AmirAlsad/beta-rush-pcb-cards/docs/order-history/jlcpcb-p3-brother-pcb-spec.png

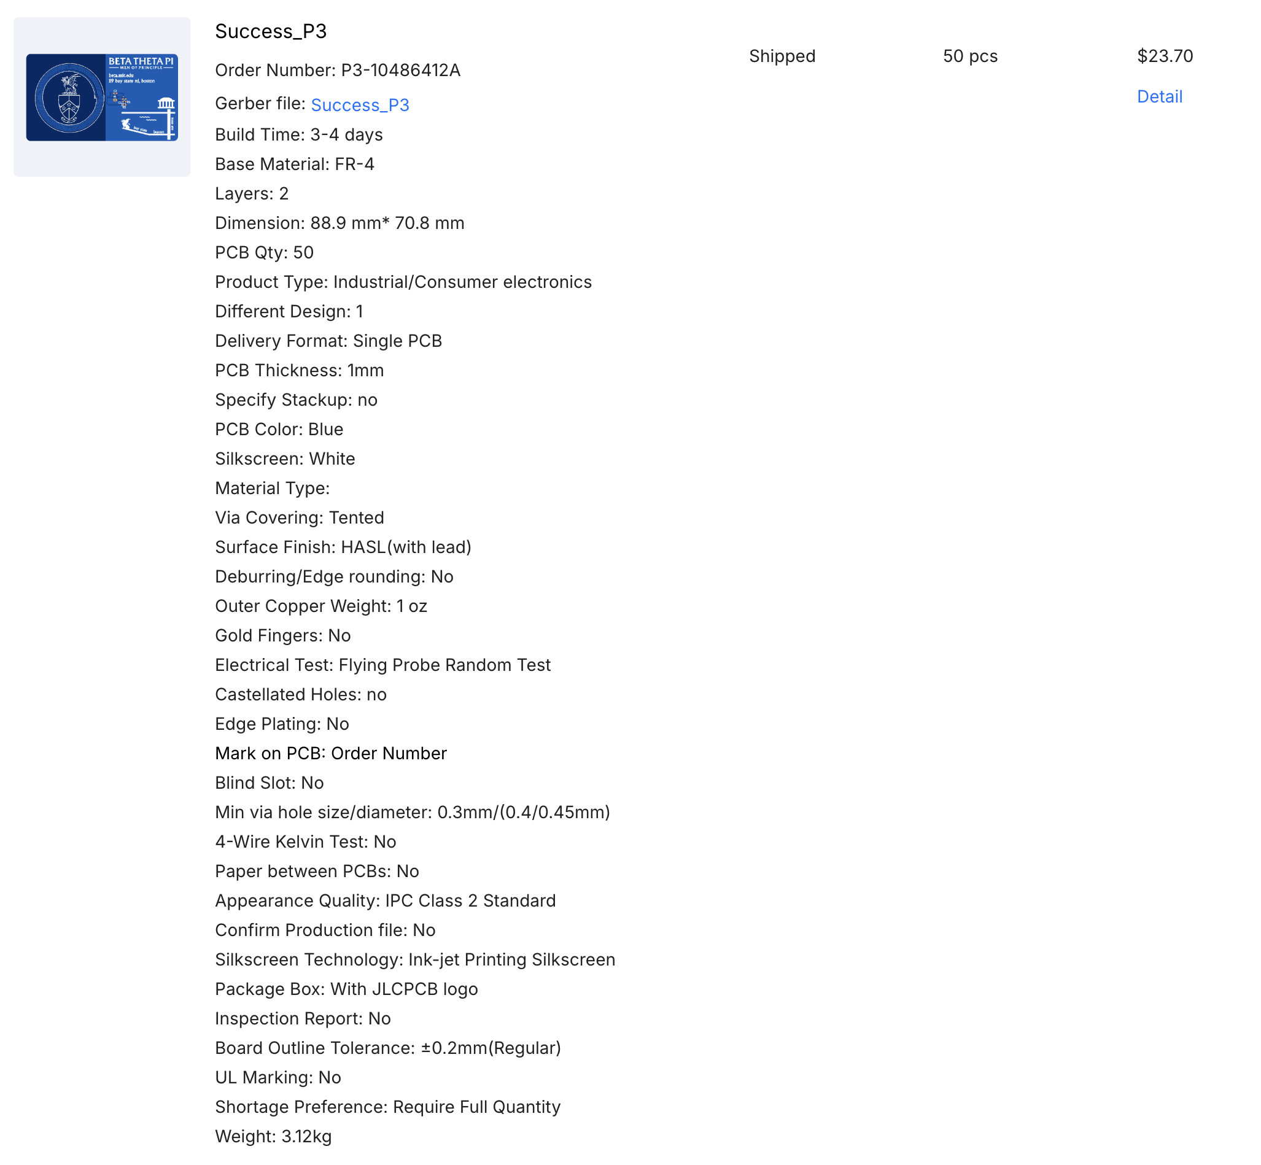
docs/order-history/jlcpcb-p3-brother-pcb-spec.png
