AmirAlsad/beta-rush-pcb-cards/docs/antenna-simulations/LTSpice_Equivalent_Circuit/NFC_LTSpice_Schematic.asc

C1: cap; 50p
C2: cap; 2p
C3: cap; 0p
L1: ind; 2.75µ
R1: res; 1.17
R2: res; 100k
V1: voltage; SINE(0 5 10); AC 1 1
Named nets: 0
.ac lin 10000 12MEG 15MEG
Rant
Lant
Cant
NFC IC Equivalence
NFC Antenna
Tuning Capacitor
